dmiddlecamp/walkie_talkies/photos/IMG_2230.JPG

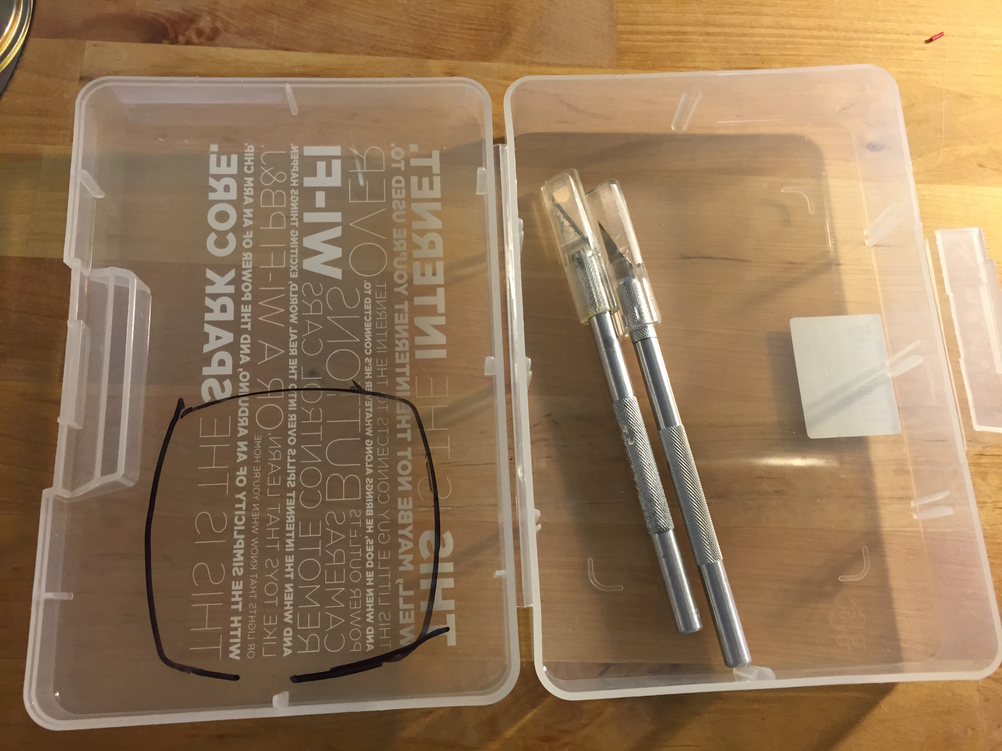
photos/IMG_2230.JPG
